Fangoboyo/carrie-shenzhen/materials/images/Pasted image 20260603153835.png

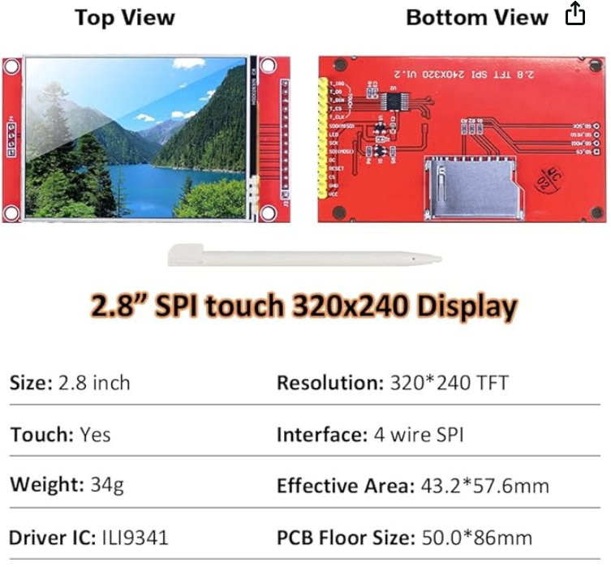
materials/images/Pasted image 20260603153835.png
