Fangoboyo/carrie-shenzhen/materials/images/Pasted image 20260603163029.png

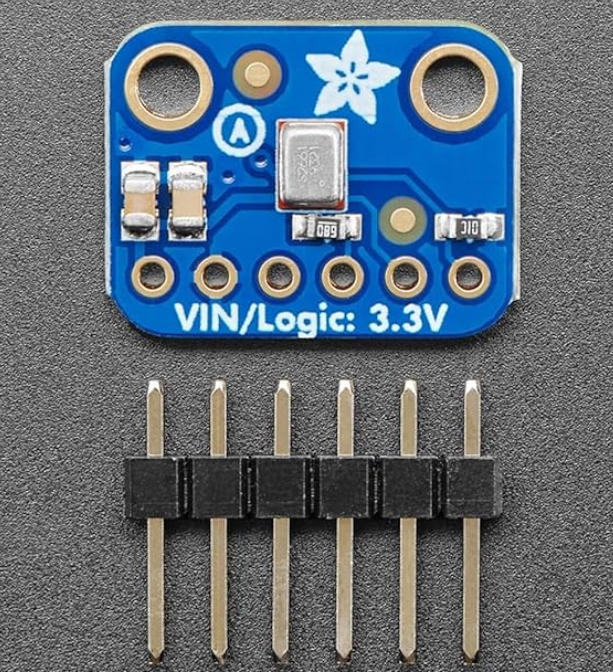
materials/images/Pasted image 20260603163029.png
