Fangoboyo/carrie-shenzhen/materials/images/Pasted image 20260604230423.png

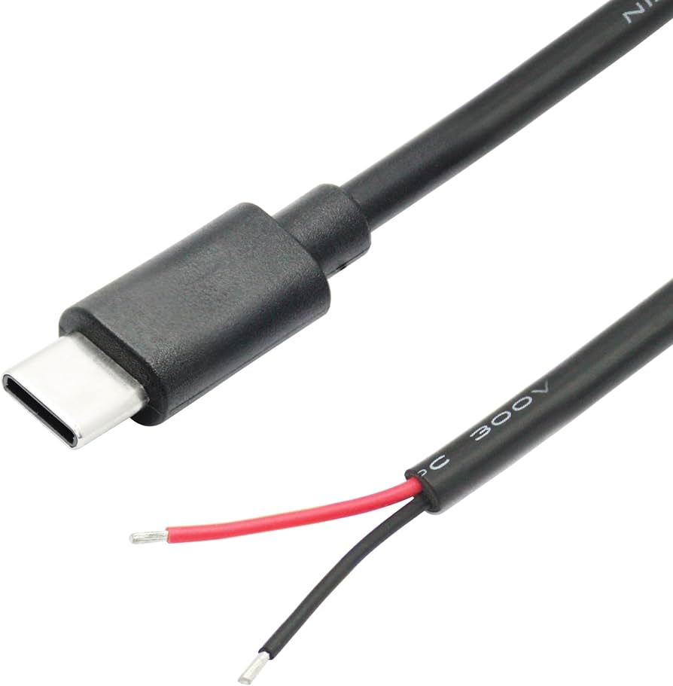
materials/images/Pasted image 20260604230423.png
