Fangoboyo/carrie-shenzhen/materials/images/Pasted image 20260604235230.png

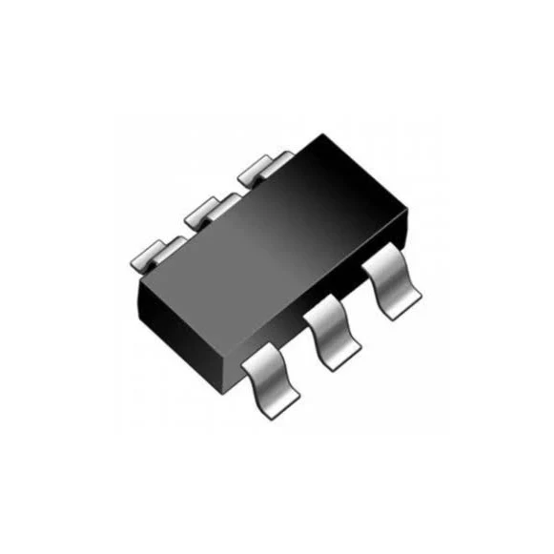
materials/images/Pasted image 20260604235230.png
