Fangoboyo/carrie-shenzhen/materials/images/Pasted image 20260604235253.png

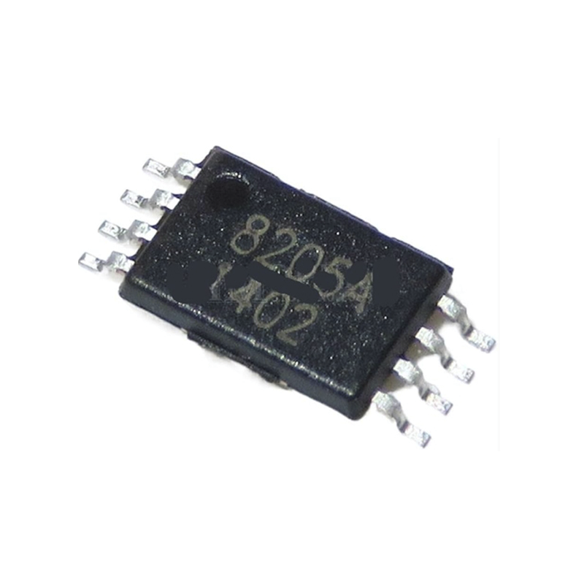
materials/images/Pasted image 20260604235253.png
