Fangoboyo/carrie-shenzhen/materials/images/Pasted image 20260605000559.png

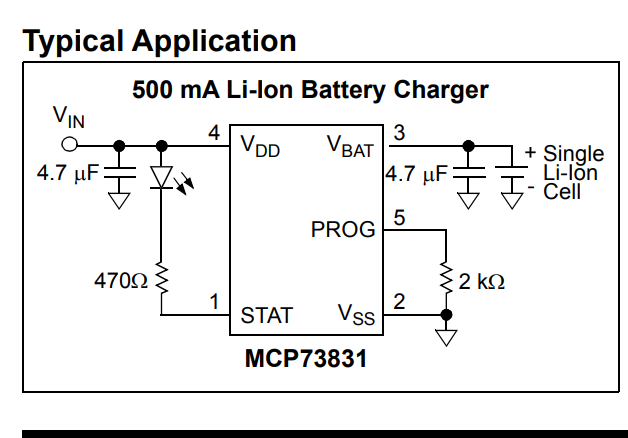
materials/images/Pasted image 20260605000559.png
